2k2e2n/macro-keyboard/dist/introduction/img2.webp

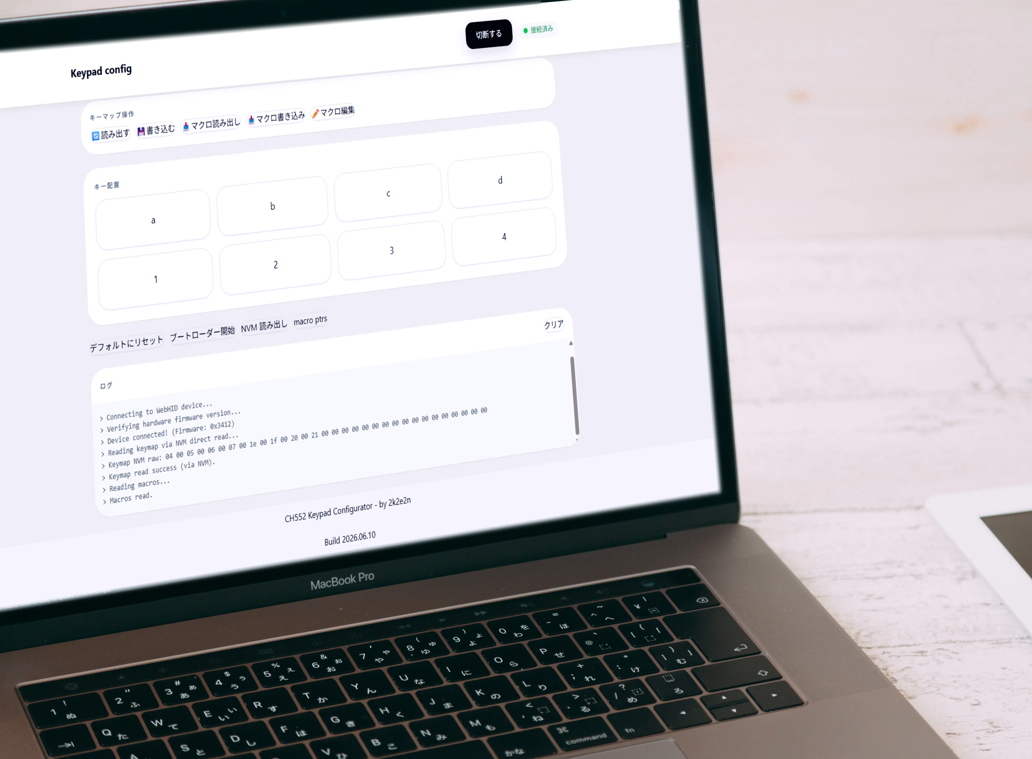
dist/introduction/img2.webp
