2k2e2n/macro-keyboard/dist/introduction/img3.webp

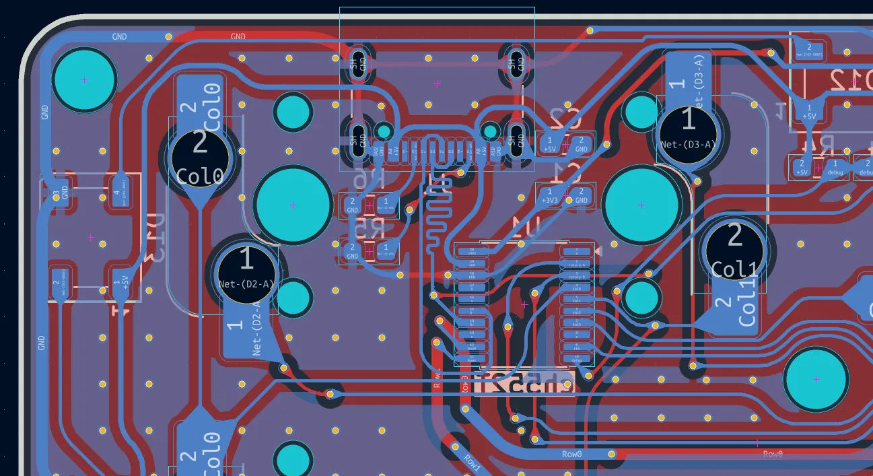
dist/introduction/img3.webp
