2k2e2n/macro-keyboard/dist/introduction/img4.webp

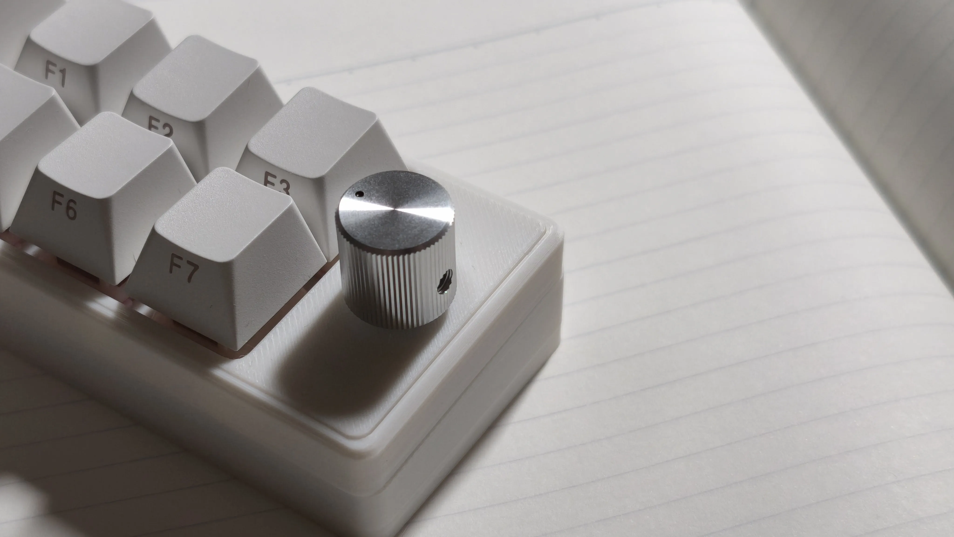
dist/introduction/img4.webp
