2k2e2n/macro-keyboard/dist/introduction/img6.webp

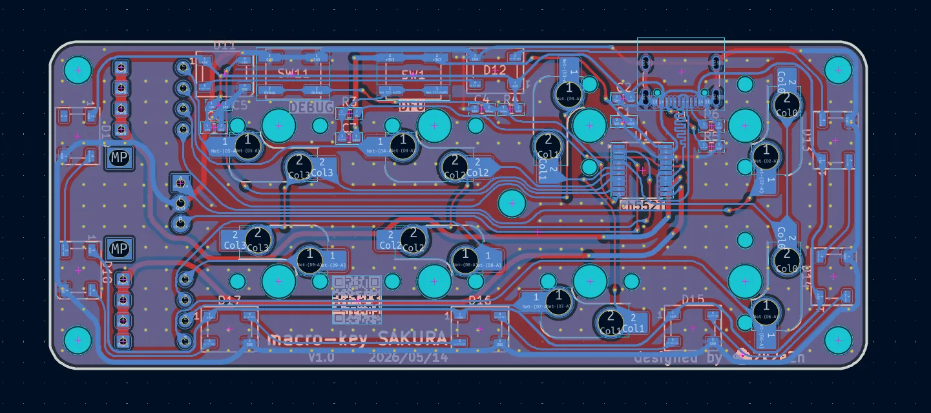
dist/introduction/img6.webp
