2k2e2n/macro-keyboard/dist/introduction/img7.webp

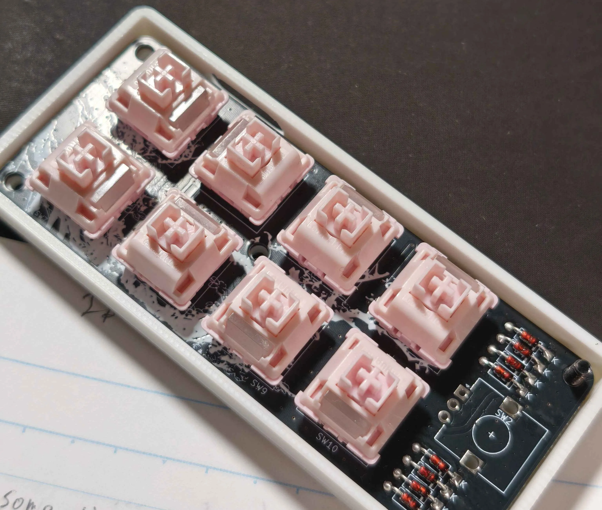
dist/introduction/img7.webp
