2k2e2n/macro-keyboard/dist/introduction/img8.webp

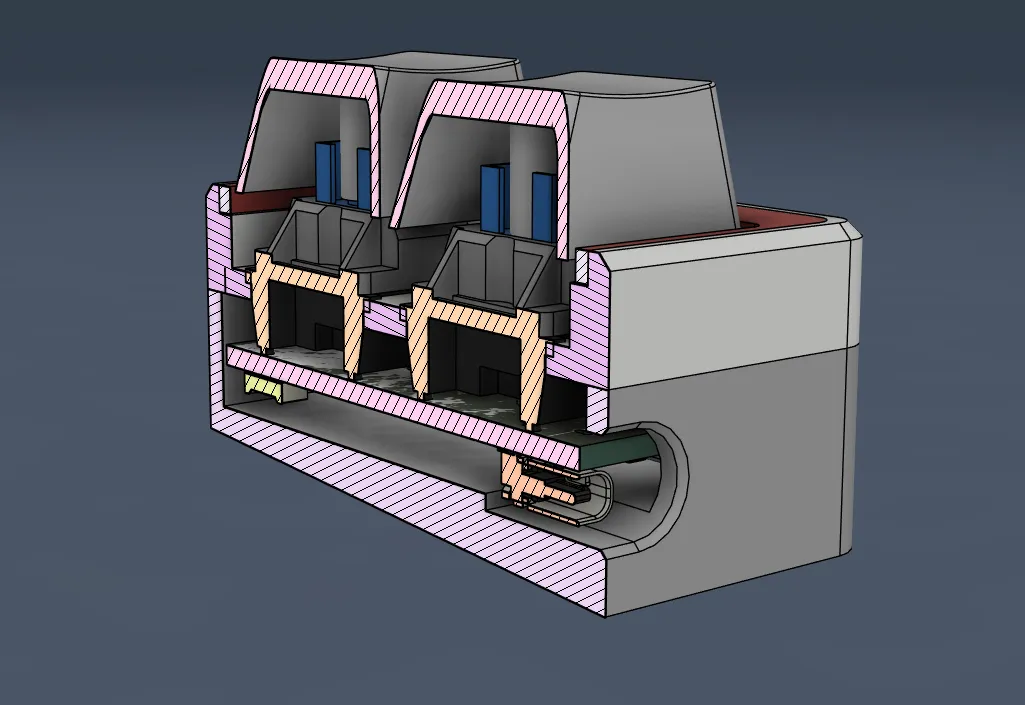
dist/introduction/img8.webp
