2k2e2n/macro-keyboard/program/ch552_keypad_Library/src/ch_usb_handler.c

/**
 * ch_usb_handler.c usb core handler of ch552g based keyboard firmware.
 * from CH55xDuino generic_examples.formly USBhandler.c.
 *
 *  created by Deqing Sun for use with CH55xduino 
 */

#include "ch_usb_handler.h"
#include "ch_usb_constant.h"

#ifndef USER_USB_RAM
#error "ch552_keypad_Library requires USER_USB_RAM to be defined in CH55xDuino board USB settings"
#endif

// Keyboard functions:

void USB_EP2_IN();
void USB_EP2_OUT();

// clang-format off
__xdata __at (EP0_ADDR) uint8_t Ep0Buffer[8];
__xdata __at (EP1_ADDR) uint8_t Ep1Buffer[128];       //on page 47 of data sheet, the receive buffer need to be min(possible packet size+2,64), IN and OUT buffer, must be even address
// clang-format on

#if (EP1_ADDR + 128) > USER_USB_RAM
#error "This example needs more USB ram. Increase this setting in menu."
#endif

__data uint16_t SetupLen;
__data uint8_t SetupReq;
volatile __xdata uint8_t UsbConfig;

__code uint8_t *__data pDescr;

volatile uint8_t usbMsgFlags = 0; // uint8_t usbMsgFlags copied from VUSB

inline void NOP_Process(void) {}

void USB_EP0_SETUP() {
	__data uint8_t len = USB_RX_LEN;
	if (len == (sizeof(USB_SETUP_REQ))) {
		SetupLen = ((uint16_t)UsbSetupBuf->wLengthH << 8) | (UsbSetupBuf->wLengthL);
		len = 0; // Default is success and upload 0 length
		SetupReq = UsbSetupBuf->bRequest;
		usbMsgFlags = 0;
		if ((UsbSetupBuf->bRequestType & USB_REQ_TYP_MASK) != USB_REQ_TYP_STANDARD) { // Not standard request
			// here is the commnunication starts, refer to usbFunctionSetup of USBtiny
			// or usb_setup in usbtiny
			switch ((UsbSetupBuf->bRequestType & USB_REQ_TYP_MASK)) {
			case USB_REQ_TYP_VENDOR:
				switch (SetupReq) {
				default:
					len = 0xFF; // command not supported
					break;
				}
				break;
			case USB_REQ_TYP_CLASS:
				switch (SetupReq) {
					default:
					len = 0xFF; // command not supported
					break;
				}
				break;
			default:
				len = 0xFF; // command not supported
				break;
			}
		} else { // Standard request
			switch (SetupReq) { // Request ccfType
			case USB_GET_DESCRIPTOR:
				switch (UsbSetupBuf->wValueH) {
				case 1: // Device Descriptor
					pDescr = (__code uint8_t *) DeviceDescriptor; // Put Device Descriptor into outgoing buffer
					len = sizeof(USB_Descriptor_Device_t);
					break;
				case 2: // Configure Descriptor
					pDescr = (__code uint8_t *)ConfigurationDescriptor;
					len = sizeof(USB_Descriptor_Configuration_t);
					break;
				case 3:
					if (UsbSetupBuf->wValueL == 0)
						pDescr = LanguageDescriptor;
					else if (UsbSetupBuf->wValueL == 1)
						pDescr = (__code uint8_t *)ManufacturerDescriptor;
					else if (UsbSetupBuf->wValueL == 2)
						pDescr = (__code uint8_t *)ProductDescriptor;
					else if (UsbSetupBuf->wValueL == 3)
						pDescr = (__code uint8_t *)SerialDescriptor;
					else {
						len = 0xff;
						break;
					}
					len = pDescr[0];
					break;
				case 0x22:
					if (UsbSetupBuf->wValueL == 0) {
						pDescr = (__code uint8_t *)ReportDescriptor;
						len = ConfigurationDescriptor.HID_KeyboardHID.HIDReportLength;
					} else
						len = 0xff;
					break;
				default:
					len = 0xff; // Unsupported descriptors or error
					break;
				}
				if (len != 0xff) {
					if (SetupLen > len) 
						SetupLen = len; // Limit length
					len = SetupLen >= DEFAULT_ENDP0_SIZE ? DEFAULT_ENDP0_SIZE : SetupLen; // transmit length for this packet
					for (__data uint8_t i = 0; i < len; i++)
						Ep0Buffer[i] = pDescr[i];
					SetupLen -= len;
					pDescr += len;
				}
				break;
			case USB_SET_ADDRESS:
				SetupLen = UsbSetupBuf->wValueL; // Save the assigned address
				break;
			case USB_GET_CONFIGURATION:
				Ep0Buffer[0] = UsbConfig;
				if (SetupLen >= 1)
					len = 1;
				break;
			case USB_SET_CONFIGURATION:
				UsbConfig = UsbSetupBuf->wValueL;
				break;
			case USB_GET_INTERFACE:
				break;
			case USB_SET_INTERFACE:
				break;
			case USB_CLEAR_FEATURE: // Clear Feature
				if ((UsbSetupBuf->bRequestType & 0x1F) ==	USB_REQ_RECIP_DEVICE) { // Clear the device featuee.
					if ((((uint16_t)UsbSetupBuf->wValueH << 8) | UsbSetupBuf->wValueL) == 0x01) {
						if (ConfigurationDescriptor.Config.ConfigAttributes & 0x20) {
							// wake up
						} else 
							len = 0xFF; // Failed
					} else
						len = 0xFF; // Failed
				} else if ((UsbSetupBuf->bRequestType & USB_REQ_RECIP_MASK) == USB_REQ_RECIP_ENDP) { // endpoint
					switch (UsbSetupBuf->wIndexL) {
					case 0x84:
						UEP4_CTRL = UEP4_CTRL & ~(bUEP_T_TOG | MASK_UEP_T_RES) | UEP_T_RES_NAK;
						break;
					case 0x04:
						UEP4_CTRL = UEP4_CTRL & ~(bUEP_R_TOG | MASK_UEP_R_RES) | UEP_R_RES_ACK;
						break;
					case 0x83:
						UEP3_CTRL = UEP3_CTRL & ~(bUEP_T_TOG | MASK_UEP_T_RES) | UEP_T_RES_NAK;
						break;
					case 0x03:
						UEP3_CTRL = UEP3_CTRL & ~(bUEP_R_TOG | MASK_UEP_R_RES) | UEP_R_RES_ACK;
						break;
					case 0x82:
						UEP2_CTRL = UEP2_CTRL & ~(bUEP_T_TOG | MASK_UEP_T_RES) | UEP_T_RES_NAK;
						break;
					case 0x02:
						UEP2_CTRL = UEP2_CTRL & ~(bUEP_R_TOG | MASK_UEP_R_RES) | UEP_R_RES_ACK;
						break;
					case 0x81:
						UEP1_CTRL = UEP1_CTRL & ~(bUEP_T_TOG | MASK_UEP_T_RES) | UEP_T_RES_NAK;
						break;
					case 0x01:
						UEP1_CTRL = UEP1_CTRL & ~(bUEP_R_TOG | MASK_UEP_R_RES) | UEP_R_RES_ACK;
						break;
					default:
						len = 0xFF; // Unsupported endpoint
						break;
					}
				} else
					len = 0xFF; // Unsupported for non-endpoint
				break;
			case USB_SET_FEATURE: // Set Feature
				if ((UsbSetupBuf->bRequestType & 0x1F) == USB_REQ_RECIP_DEVICE) { // Set  the device featuee.	
					if ((((uint16_t)UsbSetupBuf->wValueH << 8) | UsbSetupBuf->wValueL) == 0x01) {
						if (ConfigurationDescriptor.Config.ConfigAttributes & 0x20) {
						// suspend

						// while ( XBUS_AUX & bUART0_TX );    //Wait till uart0 sending
						// complete SAFE_MOD = 0x55; SAFE_MOD = 0xAA; WAKE_CTRL =
						// bWAK_BY_USB | bWAK_RXD0_LO | bWAK_RXD1_LO; //wake up by USB or
						// RXD0/1 signal PCON |= PD; //sleep SAFE_MOD = 0x55; SAFE_MOD =
						// 0xAA; WAKE_CTRL = 0x00;
						} else
							len = 0xFF; // Failed
					} else 
						len = 0xFF; // Failed
				} else if ((UsbSetupBuf->bRequestType & 0x1F) == USB_REQ_RECIP_ENDP) { // endpoint
					if ((((uint16_t)UsbSetupBuf->wValueH << 8) | UsbSetupBuf->wValueL) == 0x00) {
						switch (((uint16_t)UsbSetupBuf->wIndexH << 8) | UsbSetupBuf->wIndexL) {
						case 0x84:
							UEP4_CTRL = UEP4_CTRL & (~bUEP_T_TOG) | UEP_T_RES_STALL; // Set endpoint4 IN STALL
							break;
						case 0x04:
							UEP4_CTRL = UEP4_CTRL & (~bUEP_R_TOG) | UEP_R_RES_STALL; // Set endpoint4 OUT Stall
							break;
						case 0x83:
							UEP3_CTRL = UEP3_CTRL & (~bUEP_T_TOG) | UEP_T_RES_STALL; // Set endpoint3 IN STALL
							break;
						case 0x03:
							UEP3_CTRL = UEP3_CTRL & (~bUEP_R_TOG) | UEP_R_RES_STALL; // Set endpoint3 OUT Stall
							break;
						case 0x82:
							UEP2_CTRL = UEP2_CTRL & (~bUEP_T_TOG) | UEP_T_RES_STALL; // Set endpoint2 IN STALL
							break;
						case 0x02:
							UEP2_CTRL = UEP2_CTRL & (~bUEP_R_TOG) | UEP_R_RES_STALL; // Set endpoint2 OUT Stall
							break;
						case 0x81:
							UEP1_CTRL = UEP1_CTRL & (~bUEP_T_TOG) | UEP_T_RES_STALL; // Set endpoint1 IN STALL
							break;
						case 0x01:
							UEP1_CTRL = UEP1_CTRL & (~bUEP_R_TOG) | UEP_R_RES_STALL; // Set endpoint1 OUT Stall
							break;
						default:
							len = 0xFF; // Failed
							break;
						}
					} else
						len = 0xFF; // Failed
				} else
					len = 0xFF; // Failed
				break;
			case USB_GET_STATUS:
				Ep0Buffer[0] = 0x00;
				Ep0Buffer[1] = 0x00;
				if (SetupLen >= 2)
					len = 2;
				else
					len = SetupLen;
				break;
			default:
				len = 0xff; // Failed
				break;
			}
		}
	} else
		len = 0xff; // Wrong packet length
	if (len == 0xff) {
		SetupReq = 0xFF;
		UEP0_CTRL = bUEP_R_TOG | bUEP_T_TOG | UEP_R_RES_STALL | UEP_T_RES_STALL; // STALL
	} else if (len <= DEFAULT_ENDP0_SIZE) { // Tx data to host or send 0-length packet
		UEP0_T_LEN = len;
		UEP0_CTRL = bUEP_R_TOG | bUEP_T_TOG | UEP_R_RES_ACK | UEP_T_RES_ACK; // Expect DATA1, Answer ACK
	} else {
		UEP0_T_LEN = 0; // Tx data to host or send 0-length packet
		UEP0_CTRL = bUEP_R_TOG | bUEP_T_TOG | UEP_R_RES_ACK | UEP_T_RES_ACK; // Expect DATA1, Answer ACK
	}
}

void USB_EP0_IN() {
	switch (SetupReq) {
	__data uint8_t len ;
	case USB_GET_DESCRIPTOR:
		len = SetupLen >= DEFAULT_ENDP0_SIZE ? DEFAULT_ENDP0_SIZE : SetupLen; // send length
		for (__data uint8_t i = 0; i < len; i++)
			Ep0Buffer[i] = pDescr[i];
	// memcpy( Ep0Buffer, pDescr, len );
		SetupLen -= len;
		pDescr += len;
		UEP0_T_LEN = len;
		UEP0_CTRL ^= bUEP_T_TOG; // Switch between DATA0 and DATA1
		break;
  case USB_SET_ADDRESS:
		USB_DEV_AD = USB_DEV_AD & bUDA_GP_BIT | SetupLen;
		UEP0_CTRL = UEP_R_RES_ACK | UEP_T_RES_NAK;
		break;
	default:
		UEP0_T_LEN = 0; // End of transaction
		UEP0_CTRL = UEP_R_RES_ACK | UEP_T_RES_NAK;
		break;
	}
}

void USB_EP0_OUT() {
    UEP0_T_LEN = 0;
    UEP0_CTRL |= UEP_R_RES_ACK | UEP_T_RES_NAK; // Respond Nak
}

#pragma save
#pragma nooverlay
void USBInterrupt(void) { // inline not really working in multiple files in SDCC
	if (UIF_TRANSFER) { // Dispatch to service functions
		__data uint8_t callIndex = USB_INT_ST & MASK_UIS_ENDP;
		switch (USB_INT_ST & MASK_UIS_TOKEN) {
		case UIS_TOKEN_OUT:  // SDCC will take IRAM if array of function pointer is used.
			switch (callIndex) {
			case 0:
				EP0_OUT_Callback();
				break;
			case 1:
				EP1_OUT_Callback();
				break;
			case 2:
				EP2_OUT_Callback();
				break;
			case 3:
				EP3_OUT_Callback();
				break;
			case 4:
				EP4_OUT_Callback();
				break;
			default:
				break;
			}
			break;
		case UIS_TOKEN_SOF: 	// SDCC will take IRAM if array of function pointer is used.
			switch (callIndex) {
			case 0:
				EP0_SOF_Callback();
				break;
			case 1:
				EP1_SOF_Callback();
				break;
			case 2:
				EP2_SOF_Callback();
				break;
			case 3:
				EP3_SOF_Callback();
				break;
			case 4:
				EP4_SOF_Callback();
				break;
			default:
				break;
			}
			break;
		case UIS_TOKEN_IN: // SDCC will take IRAM if array of function pointer is used.
			switch (callIndex) {
			case 0:
				EP0_IN_Callback();
				break;
			case 1:
				EP1_IN_Callback();
				break;
			case 2:
				EP2_IN_Callback();
				break;
			case 3:
				EP3_IN_Callback();
				break;
			case 4:
				EP4_IN_Callback();
				break;
			default:
				break;
			}
			break;
		case UIS_TOKEN_SETUP: // SDCC will take IRAM if array of function pointer is used.
			switch (callIndex) {
			case 0:
				EP0_SETUP_Callback();
				break;
			case 1:
				EP1_SETUP_Callback();
				break;
			case 2:
				EP2_SETUP_Callback();
				break;
			case 3:
				EP3_SETUP_Callback();
				break;
			case 4:
				EP4_SETUP_Callback();
				break;
			default:
				break;
			}
			break;
		}
		UIF_TRANSFER = 0; // Clear interrupt flag
	}

	// Device mode USB bus reset
	if (UIF_BUS_RST) {
		UEP0_CTRL = UEP_R_RES_ACK | UEP_T_RES_NAK;
		UEP1_CTRL = bUEP_AUTO_TOG | UEP_T_RES_NAK | UEP_R_RES_ACK;

		USB_DEV_AD = 0x00;
		UIF_SUSPEND = 0;
		UIF_TRANSFER = 0;
		UIF_BUS_RST = 0;

		UsbConfig = 0;
		// Clear interrupt flag
	}

	// USB bus suspend / wake up
  if (UIF_SUSPEND) {
		UIF_SUSPEND = 0;
		if (USB_MIS_ST & bUMS_SUSPEND) { // Enable suspend.
#if 1
			USBStartSuspend();	// call main sketch to turn off LED.
			SAFE_MOD = 0x55;
			SAFE_MOD = 0xAA;
			WAKE_CTRL = bWAK_BY_USB;    // Wake up by USB or RxD0
			PCON |= PD;
#endif
		} else {             // Unexpected interrupt, not supposed to happen !
			USB_INT_FG = 0xFF; // Clear interrupt flag
		}
	}
}
#pragma restore

void USBDeviceCfg() {
	USB_CTRL = 0x00;            // Clear USB control register
	USB_CTRL &= ~bUC_HOST_MODE; // This bit is the device selection mode
	USB_CTRL |= bUC_DEV_PU_EN | bUC_INT_BUSY | bUC_DMA_EN; 
					// USB device and internal pull-up enable,
					// automatically return to NAK before interrupt flag
					// is cleared during interrupt
	USB_DEV_AD = 0x00;      // Device address initialization
	//     USB_CTRL |= bUC_LOW_SPEED;
	//     UDEV_CTRL |= bUD_LOW_SPEED; //Run for 1.5M
	USB_CTRL &= ~bUC_LOW_SPEED;
	UDEV_CTRL &= ~bUD_LOW_SPEED; // Select full speed 12M mode, default mode
#if defined(CH551) || defined(CH552) || defined(CH549)
	UDEV_CTRL = bUD_PD_DIS; // Disable DP/DM pull-down resistor
#endif
#if defined(CH559)
	UDEV_CTRL = bUD_DP_PD_DIS; // Disable DP/DM pull-down resistor
#endif
	UDEV_CTRL |= bUD_PORT_EN; // Enable physical port
}

void USBDeviceIntCfg() {
	USB_INT_EN |= bUIE_SUSPEND;  // Enable device hang interrupt
	USB_INT_EN |= bUIE_TRANSFER; // Enable USB transfer completion interrupt
	USB_INT_EN |= bUIE_BUS_RST;  // Enable device mode USB bus reset interrupt
	USB_INT_FG |= 0x1F;          // Clear interrupt flag
	IE_USB = 1;                  // Enable USB interrupt
	EA = 1;                      // Enable global interrupts
}

void USBDeviceEndPointCfg() {
#if defined(CH559)
// CH559 use differend endianness for these registers
	UEP0_DMA_H = ((uint16_t)Ep0Buffer >> 8); // Endpoint 0 data transfer address
	UEP0_DMA_L = ((uint16_t)Ep0Buffer >> 0); // Endpoint 0 data transfer address
	UEP1_DMA_H = ((uint16_t)Ep1Buffer >> 8); // Endpoint 1 data transfer address
	UEP1_DMA_L = ((uint16_t)Ep1Buffer >> 0); // Endpoint 1 data transfer address
#else
	UEP0_DMA = (uint16_t)Ep0Buffer; // Endpoint 0 data transfer address
	UEP1_DMA = (uint16_t)Ep1Buffer; // Endpoint 1 data transfer address
#endif

	UEP1_CTRL = bUEP_AUTO_TOG | UEP_T_RES_NAK | UEP_R_RES_ACK; 
		// Endpoint 2 automatically flips the sync flag, IN transaction returns NAK, OUT returns ACK
	UEP4_1_MOD = 0XC0;	// endpoint1 TX RX enable
	UEP0_CTRL = UEP_R_RES_ACK | UEP_T_RES_NAK; // Manual flip, OUT transaction returns
                                     // ACK, IN transaction returns NAK
}
