2k2e2n/macro-keyboard/program/ch552_keypad_Library/src/hid_raw_request.c

/**
 * hid_raw_request.c HID raw request handling (webhid) part of keyboard program using ch552g.
 * Copyright (c)  Takeshi Higasa, okiraku-camera.tokyo
 * 
 * This software is released under the MIT License.
 * http://opensource.org/licenses/mit-license.php
 * 
 */

#include "Arduino.h"
#include "nvm_keymap.h"	

extern void enter_bootloader_mode();

#define VERSION_NUM 0x1234
#define GET_VERSION		1

#define STARTBOOT_LOADER	0x0c
#define READ_NVM			0x0a
#define READ_MACRO_PTRS		0x0b

#define RESET_KEYMAP	0x10
#define READ_KEY		0x11
#define WRITE_KEY		0x12
#define READ_KEYMAP		0x15
#define WRITE_KEYMAP	0x16
#define READ_MACROS		0x18
#define WRITE_MACROS	0x19
#define WRITE_RE_KEYS	0x1c
#define READ_RE_KEYS	0x1d	

//
int8_t raw_input(uint8_t* data) {
	uint16_t bytes = 0;
	if (data) {
		switch(*data) {
		case RESET_KEYMAP:		
		// init nvm keymap and return version nuumber.
			reset_nvm();
			// thgough
		case GET_VERSION:
			data[1] = VERSION_NUM & 0xFF;  // lower
			data[2] = (VERSION_NUM >> 8) & 0xFF;  // upper
			bytes = 2;
			break;
		case READ_KEY:		
		// read single keycode from nvm 
		// data[1] : switch no, data[2] : layer no,
			bytes = read_nvm_code(data[1], data[2]);
			data[1] = bytes & 0xFF; // lower
			data[2] = (bytes >> 8) & 0xFF; // upper
			bytes = 2;
			break;
		case WRITE_KEY:		
		// write single keycode to nvm.
		// data[1] : switch no, data[2] : layer no, data[3] : lower byte, data[4] : upper byte
			write_nvm_code(data[1], data[2], (uint16_t)(data[3] + (data[4] << 8))); 
			data[1] = 1;
			bytes = 1;
			break;
		case READ_KEYMAP:	
		// read keymap of nvm.
		// data[1] : start switch no, data[2] : number of switches, data[3] : layer no, keycodes are stored after data[4].
			bytes = read_keys(data[1], data[2], data[3], (uint16_t*)&data[4]);
			data[1] = bytes; // number of switches read.
			bytes = 1;
			break;
		case WRITE_KEYMAP:
		// write keymap to nvm.
			bytes = write_keys(data[1], data[2], data[3], (uint16_t*)&data[4]); // 1 key = 2 bytes
			data[1] = bytes; // number of switches written. keycodes are stored after data[4].
			break;
		case READ_MACROS:
			// data[1] : start address (0~), data[2] : number of bytes, data[3] onwards : macro code string. 
			bytes = read_macros(data[1], data[2], (char*)&data[3]); 
			data[1] = bytes; // number of bytes read. macro code string is stored after data[3].
			break;
		case WRITE_MACROS:
			// write macro code. data[1] : start index, data[2] : number of bytes, data[3] onwards : macro code string.
			bytes = write_macros(data[1], data[2], (char*)&data[3]);
			data[1] = bytes; // number of bytes written.
			break;
		case STARTBOOT_LOADER:
			enter_bootloader_mode();
			break;
		case WRITE_RE_KEYS:
			// write RE keys. data[1] : RE number, data[2] : layer number, data[3] : re count, data[4] : buffer address containing 16-bit codes in CW, CCW order
			bytes = write_re_keys(data[1], data[2], data[3], (uint16_t*)&data[4]);
			data[1] = bytes; // number of bytes written.
			break;
		case READ_RE_KEYS:
			// read RE keys. data[1] : RE number, data[2] : layer number, data[3] : re count, data[4] : buffer address to store 16-bit codes in CW, CCW order
			bytes = read_re_keys(data[1], data[2], data[3], (uint16_t*)&data[4]);
			data[1] = bytes; // number of bytes read.
			break;
		case READ_NVM:
			// read nvm block to buffer. data[1] : start address, data[2] : number of bytes, data[3] onwards : buffer to store read bytes.
			bytes = read_nvm_block(data[1], data[2], (uint8_t*)&data[2]);
			data[1] = bytes; // number of bytes read.
			break;	
		case READ_MACRO_PTRS:	// for debug.
			bytes = read_macro_ptrs(data[1], (uint8_t*)&data[2]);
			data[1] = bytes; // number of bytes read.
			break;
		default:
			data[1] = 0xde; 
			data[2] = 0xad;
			bytes = 2;
			break;
		}
	}
	return bytes;
}
